guyjeangilles/raspswitch-mirror/images/partial_audio_power_circuit.jpg

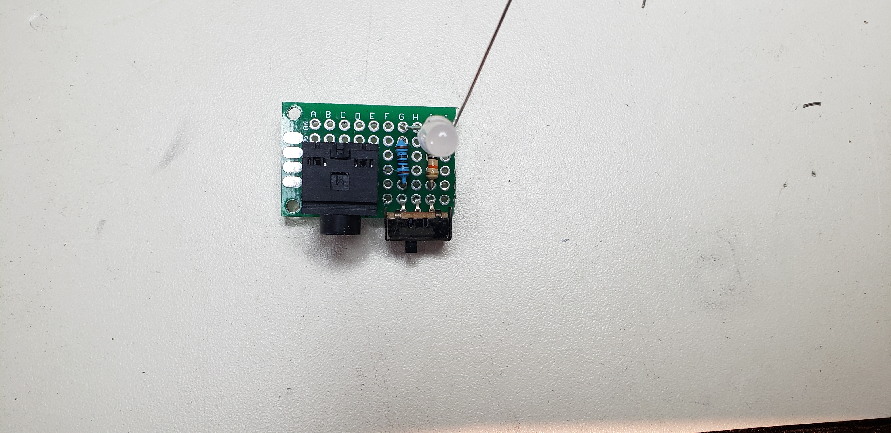
images/partial_audio_power_circuit.jpg
