guyjeangilles/raspswitch-mirror/STLs/G0011_catch_and_release_enclosure.STL

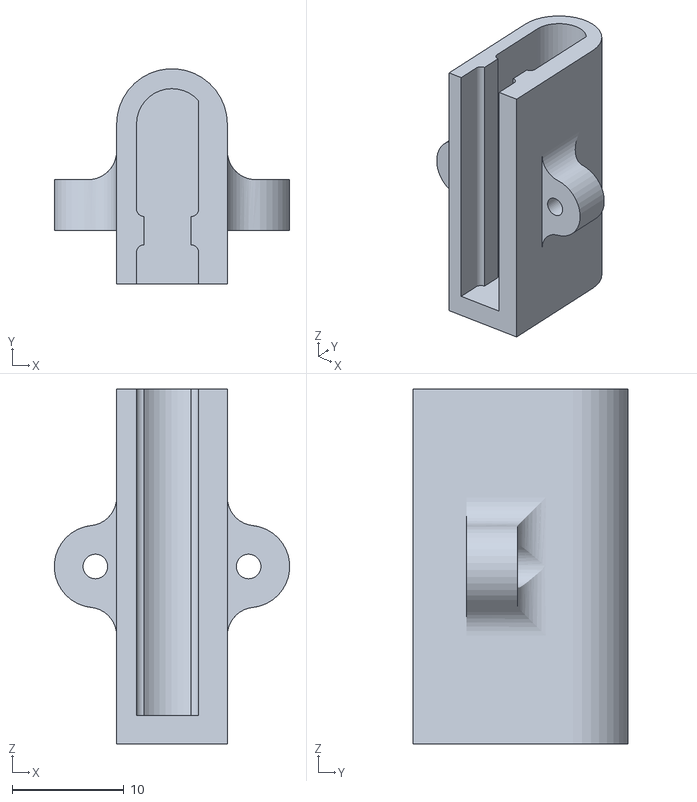
[picture p65: CAD file, 2019-10-08]
STLs/G0011_catch_and_release_enclosure.STL
21.0 x 19.2 x 31.8
