guyjeangilles/raspswitch-mirror/STEP AP203/dum_battery.step

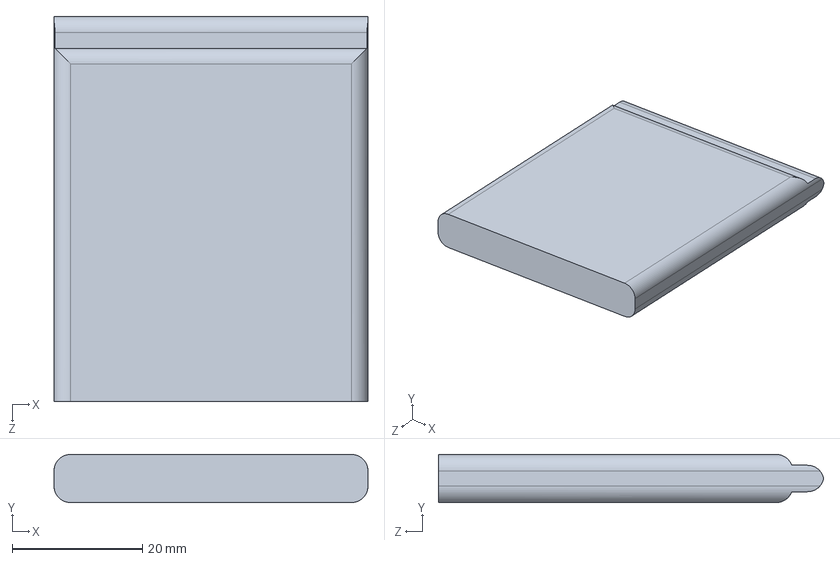
[picture p66: CAD file, 2019-10-08]
STEP AP203/dum_battery.step
48.1 x 7.38 x 59.1 mm
