guyjeangilles/raspswitch-mirror/STEP AP214/G0010_gamepad_left_top.step

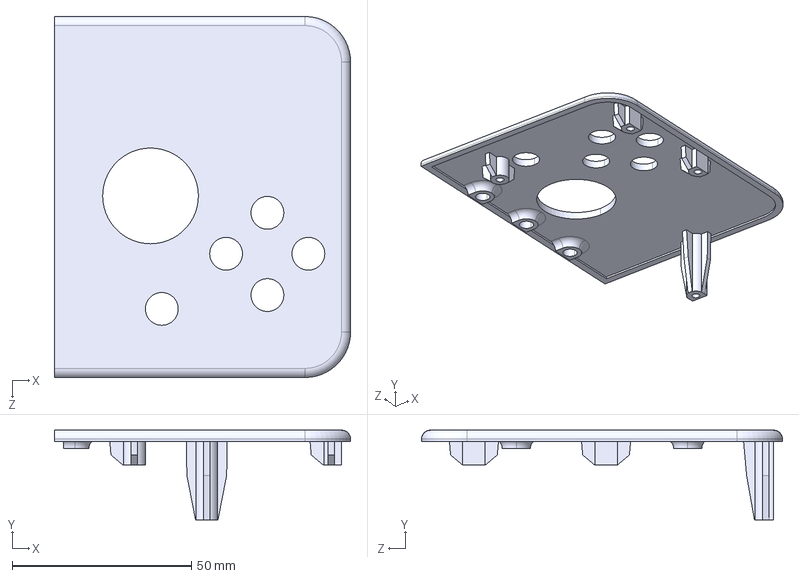
[picture p67: CAD file, 2019-10-08]
STEP AP214/G0010_gamepad_left_top.step
82.5 x 25.0 x 100.6 mm
