guyjeangilles/raspswitch-mirror/STLs/G002_dual_shaft_cap.STL

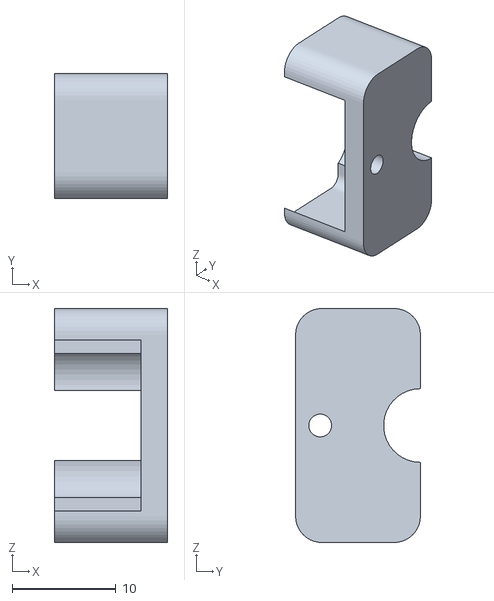
[picture p68: CAD file, 2019-10-08]
STLs/G002_dual_shaft_cap.STL
10.9 x 12.1 x 22.6
