guyjeangilles/raspswitch-mirror/STEP AP203/Molex2pinSMD.step

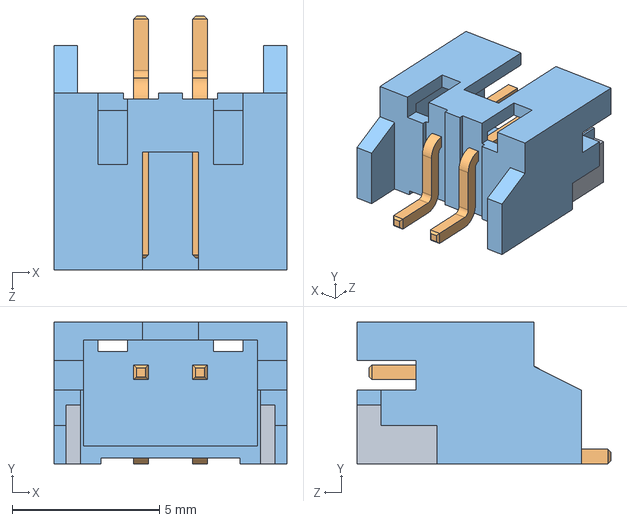
[picture p69: CAD file, 2019-10-08]
STEP AP203/Molex2pinSMD.step
7.90 x 4.80 x 8.60 mm
