guyjeangilles/raspswitch-mirror/STLs/G0009_gamepad_right_top.STL

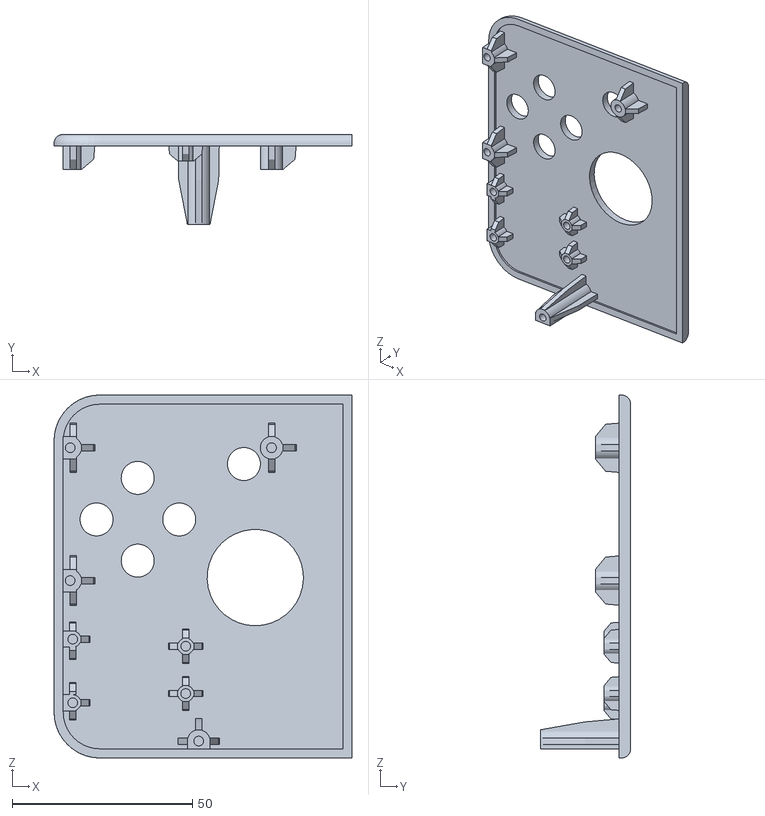
[picture p70: CAD file, 2019-10-08]
STLs/G0009_gamepad_right_top.STL
82.5 x 25.0 x 100.6
