guyjeangilles/raspswitch-mirror/STEP AP203/G0012_face_button.step

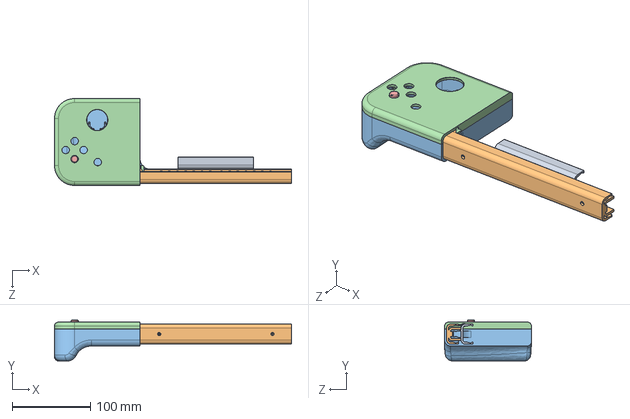
[picture p71: CAD file, 2019-10-08]
STEP AP203/G0012_face_button.step
302.3 x 52.1 x 110.8 mm
