guyjeangilles/raspswitch-mirror/STEP AP214/3.5mm_headphone_jack.step

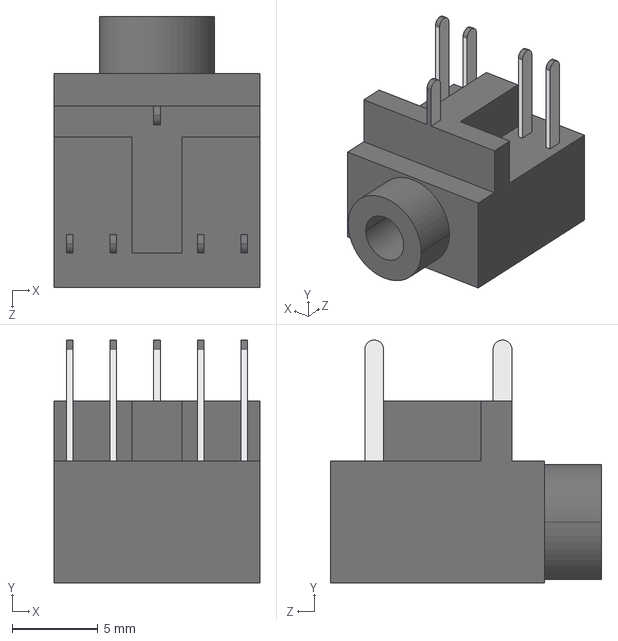
[picture p72: CAD file, 2019-10-08]
STEP AP214/3.5mm_headphone_jack.step
12.0 x 14.2 x 15.8 mm
