guyjeangilles/raspswitch-mirror/STLs/C001_top_case.STL

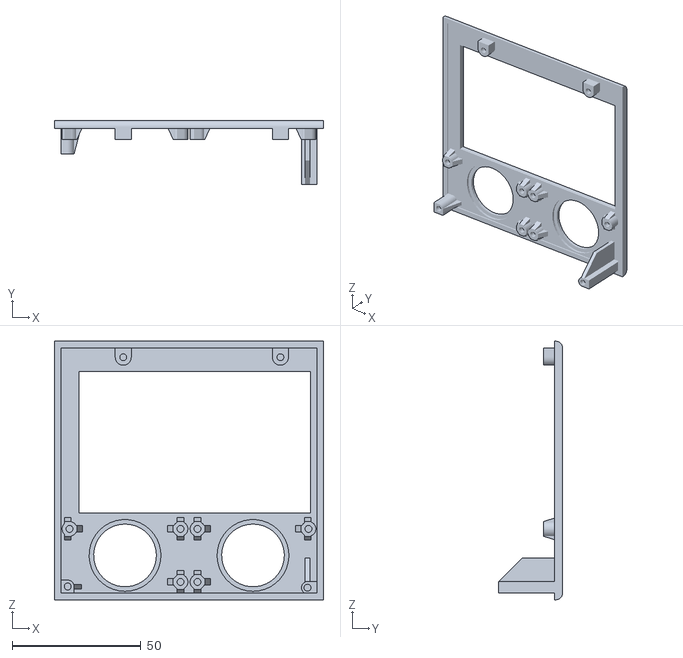
[picture p73: CAD file, 2019-10-08]
STLs/C001_top_case.STL
104.6 x 24.9 x 100.6
