guyjeangilles/raspswitch-mirror/STEP AP203/SW_PUSH_8mm002.step

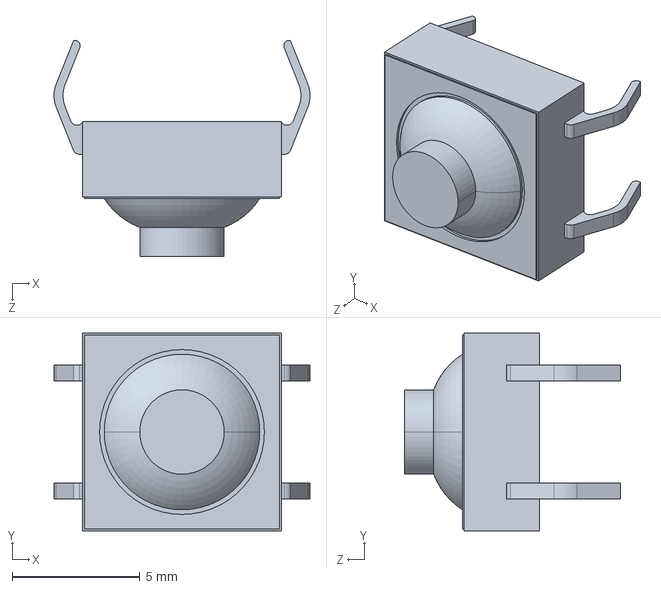
[picture p74: CAD file, 2019-10-08]
STEP AP203/SW_PUSH_8mm002.step
10.0 x 7.75 x 8.46 mm
