guyjeangilles/raspswitch-mirror/STEP AP214/stackable_header.step

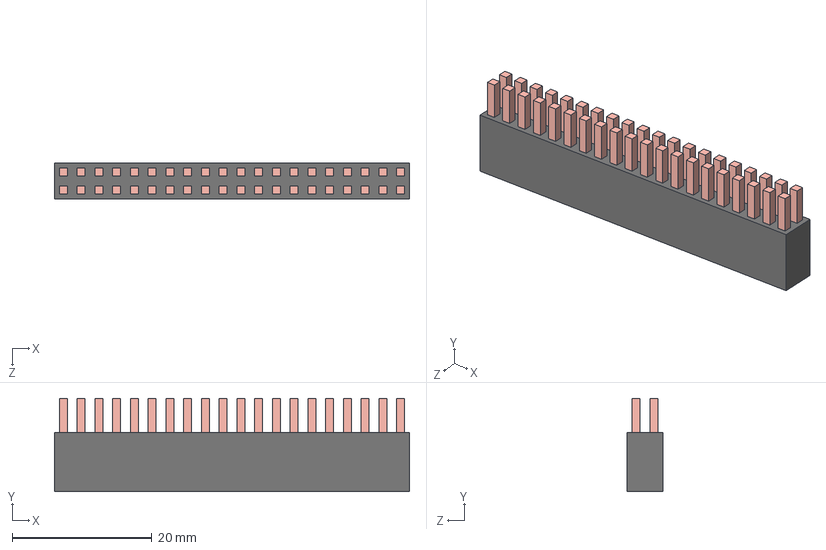
[picture p75: CAD file, 2019-10-08]
STEP AP214/stackable_header.step
50.8 x 13.3 x 5.08 mm
