guyjeangilles/raspswitch-mirror/STLs/G001_dual_shaft_bay.STL

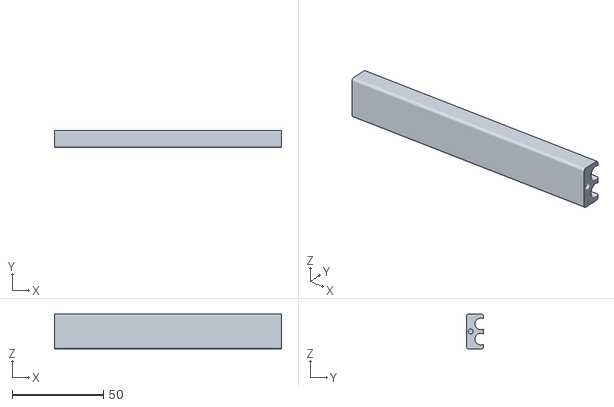
[picture p76: CAD file, 2019-10-08]
STLs/G001_dual_shaft_bay.STL
124.5 x 9.53 x 19.1
