guyjeangilles/raspswitch-mirror/STEP AP203/micro usb shell.step

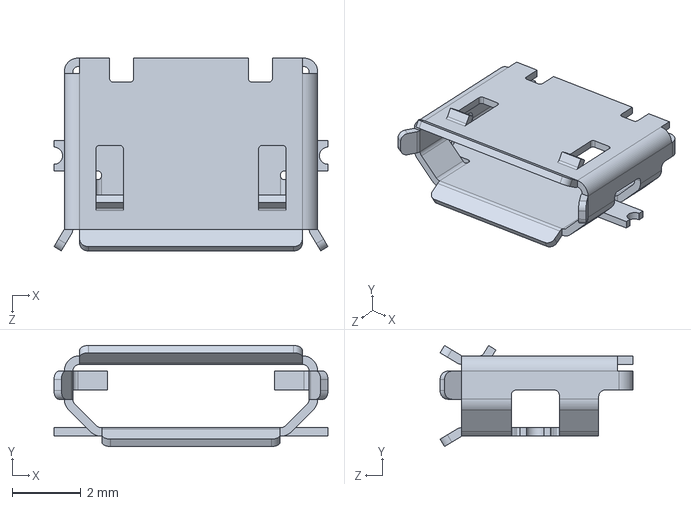
[picture p77: CAD file, 2019-10-08]
STEP AP203/micro usb shell.step
8.00 x 2.95 x 5.63 mm
