guyjeangilles/raspswitch-mirror/STLs/G0003_gamepad_left_bottom.STL

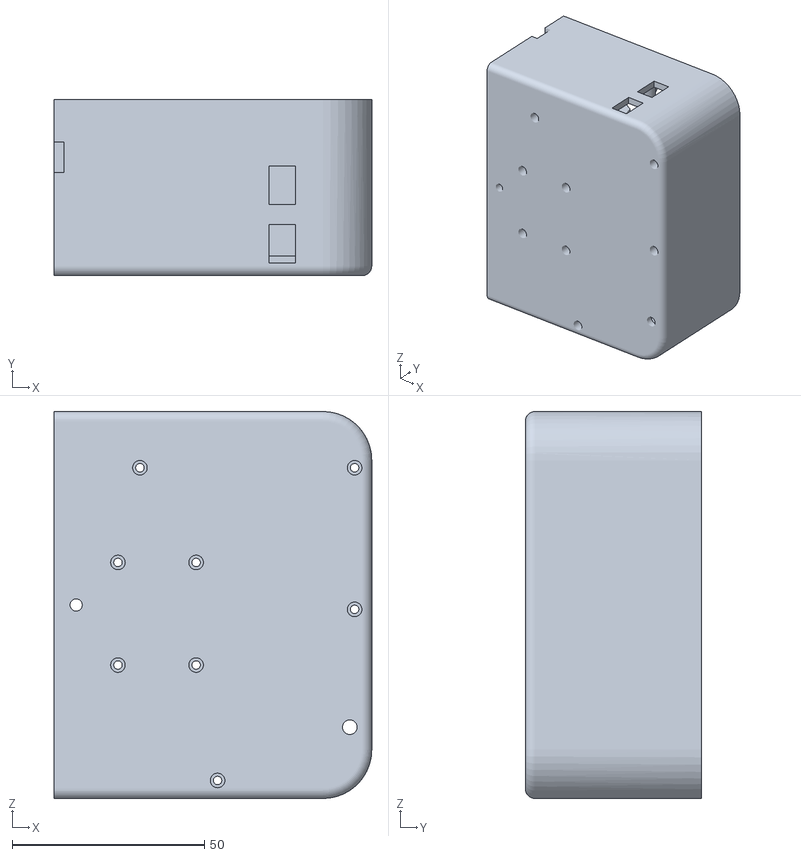
[picture p78: CAD file, 2019-10-08]
STLs/G0003_gamepad_left_bottom.STL
82.5 x 45.9 x 100.6
