guyjeangilles/raspswitch-mirror/STEP AP203/micro solid tantalum cap 22u.step

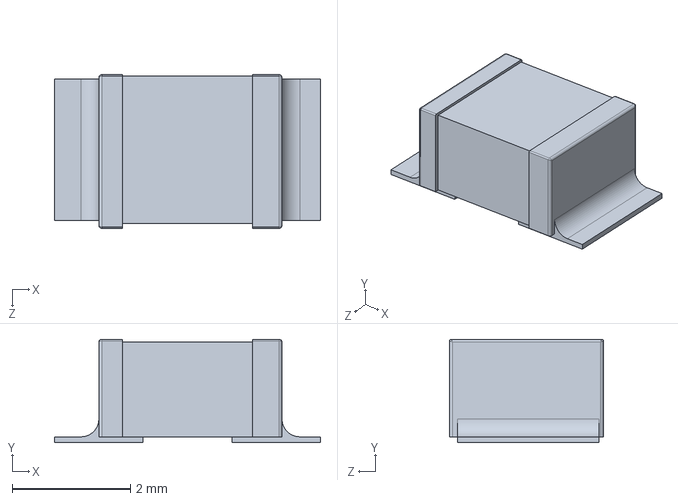
[picture p79: CAD file, 2019-10-08]
STEP AP203/micro solid tantalum cap 22u.step
4.50 x 1.75 x 2.60 mm
