guyjeangilles/raspswitch-mirror/STEP AP214/G0008_release_slide.step

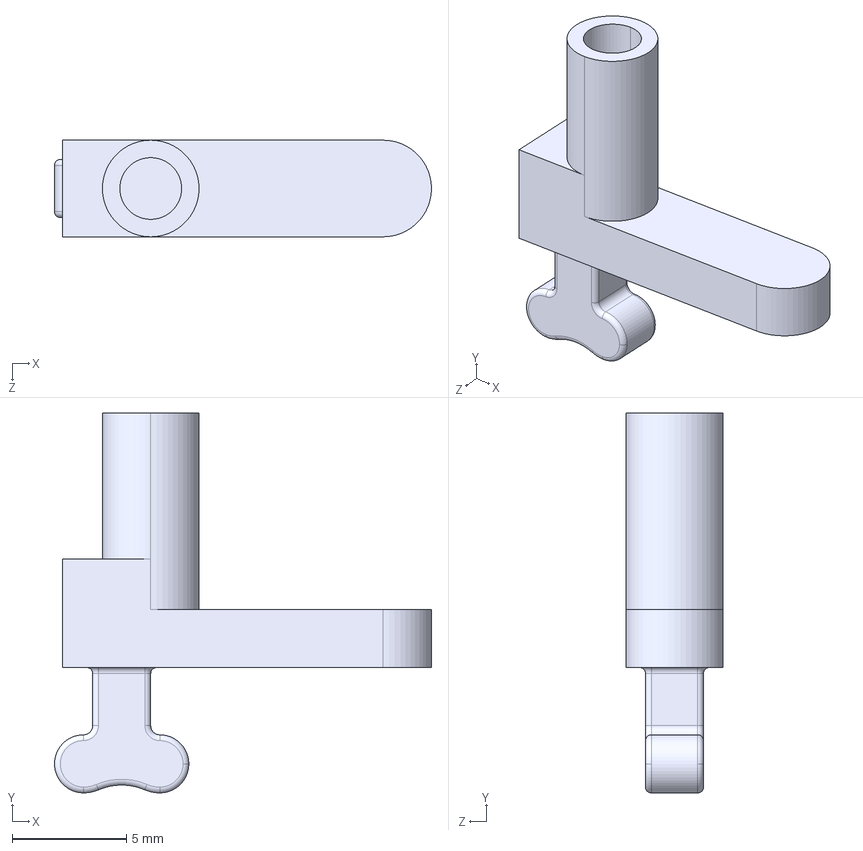
[picture p80: CAD file, 2019-10-08]
STEP AP214/G0008_release_slide.step
16.5 x 16.6 x 4.22 mm
