guyjeangilles/raspswitch-mirror/STEP AP203/speaker.step

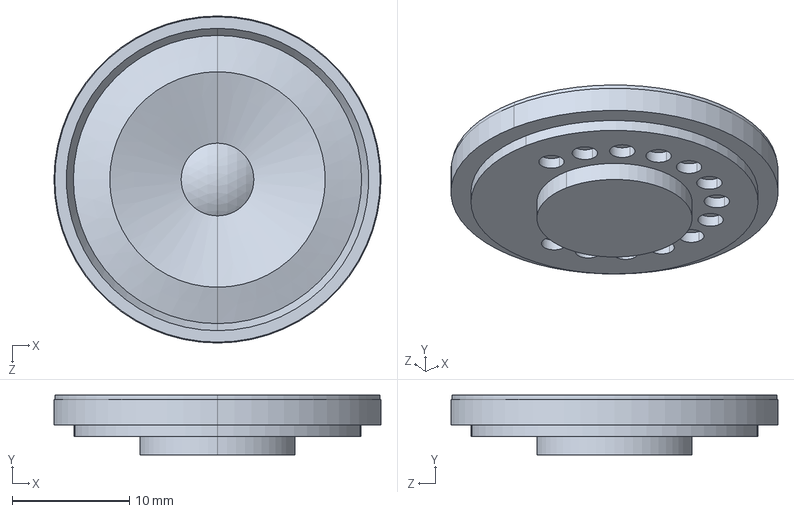
[picture p81: CAD file, 2019-10-08]
STEP AP203/speaker.step
27.9 x 5.12 x 27.9 mm
