guyjeangilles/raspswitch-mirror/STEP AP203/micro RESET.step

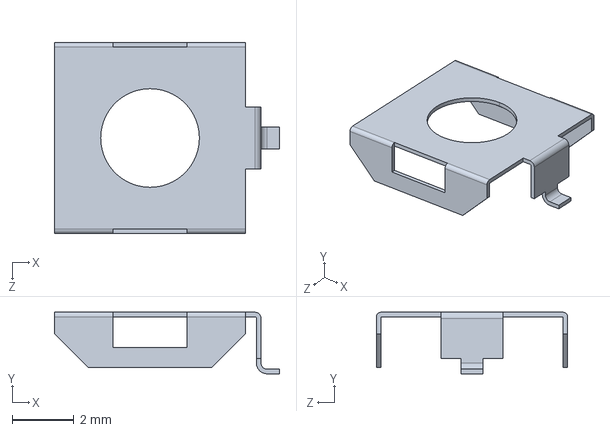
[picture p82: CAD file, 2019-10-08]
STEP AP203/micro RESET.step
7.30 x 2.00 x 6.20 mm
