guyjeangilles/raspswitch-mirror/STLs/G0004_console_catch.STL

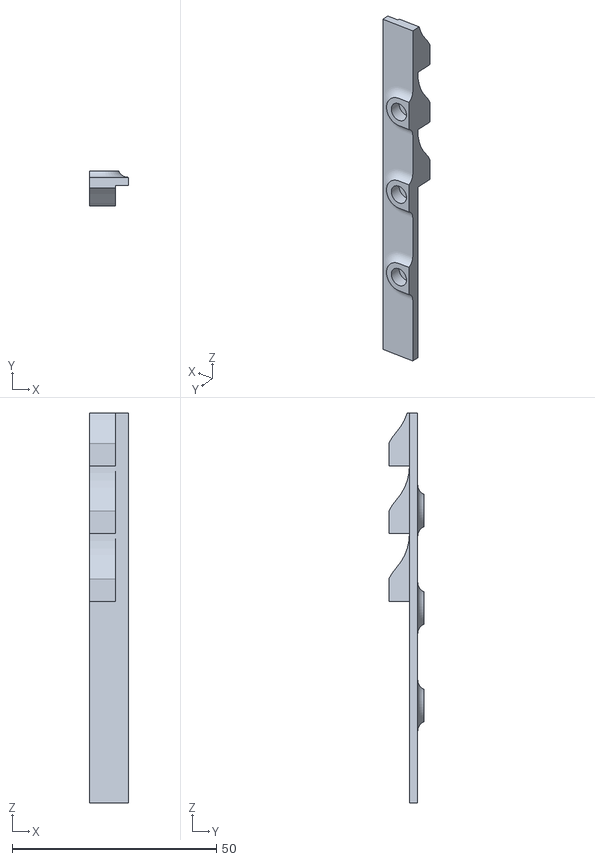
[picture p83: CAD file, 2019-10-08]
STLs/G0004_console_catch.STL
9.53 x 8.67 x 95.5
