guyjeangilles/raspswitch-mirror/STEP AP203/COMPOUND0.step

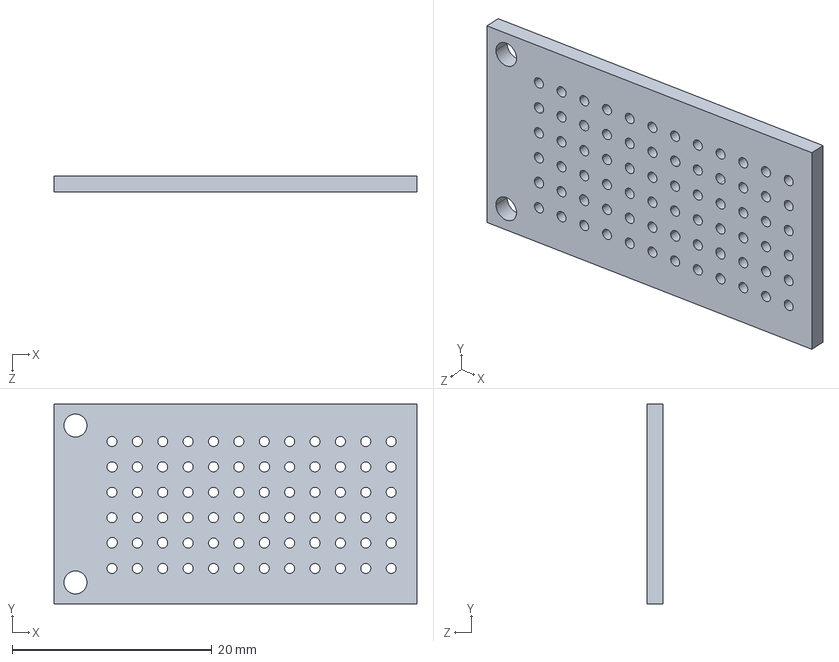
[picture p84: CAD file, 2019-10-08]
STEP AP203/COMPOUND0.step
36.3 x 20.0 x 1.60 mm
