guyjeangilles/raspswitch-mirror/STEP AP214/micro_crystal 3.2 x 2.5.step

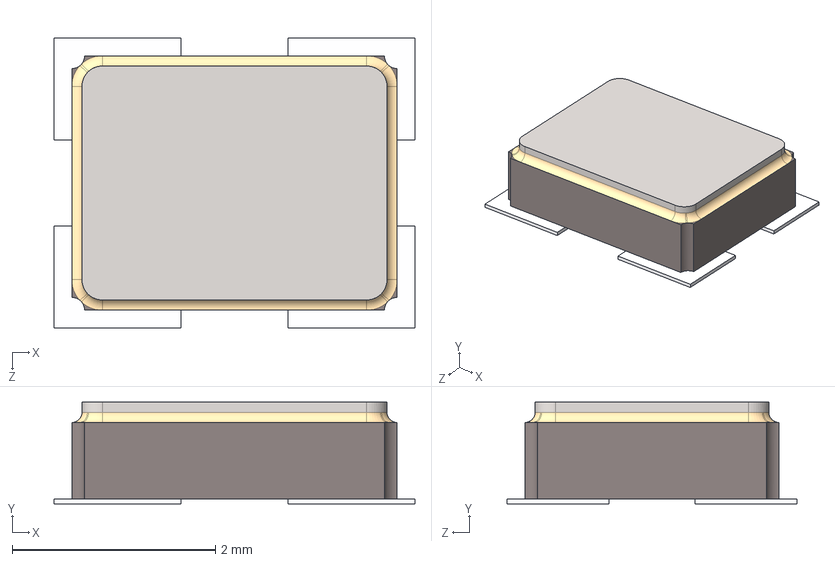
[picture p85: CAD file, 2019-10-08]
STEP AP214/micro_crystal 3.2 x 2.5.step
3.55 x 1.00 x 2.85 mm
