guyjeangilles/raspswitch-mirror/STLs/G0007_gamepad_right_bottom.STL

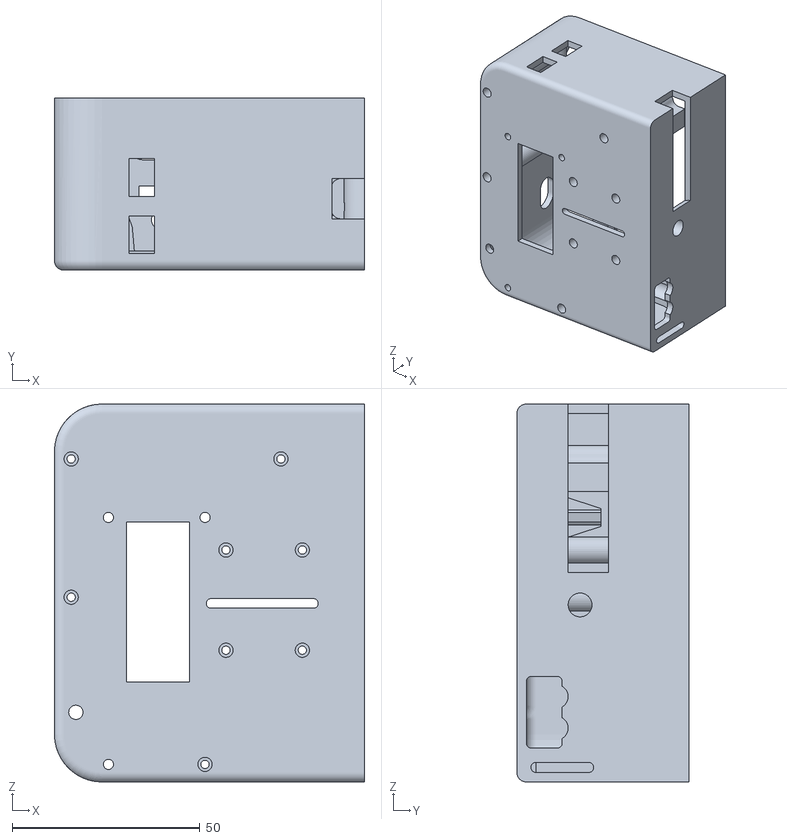
[picture p86: CAD file, 2019-10-08]
STLs/G0007_gamepad_right_bottom.STL
82.5 x 45.9 x 100.6
