guyjeangilles/raspswitch-mirror/STEP AP214/cut_2cmX8cm_protoboard.step

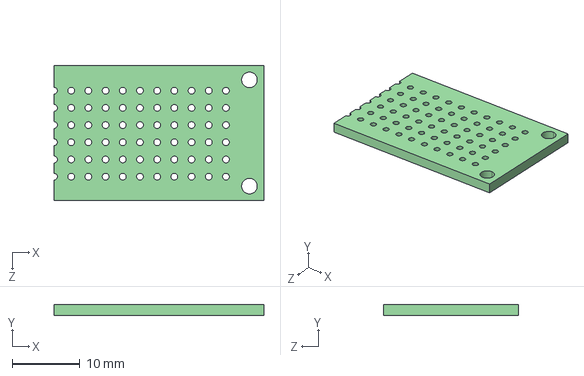
[picture p87: CAD file, 2019-10-08]
STEP AP214/cut_2cmX8cm_protoboard.step
31.0 x 1.60 x 20.0 mm
