guyjeangilles/raspswitch-mirror/STEP AP214/9032.step

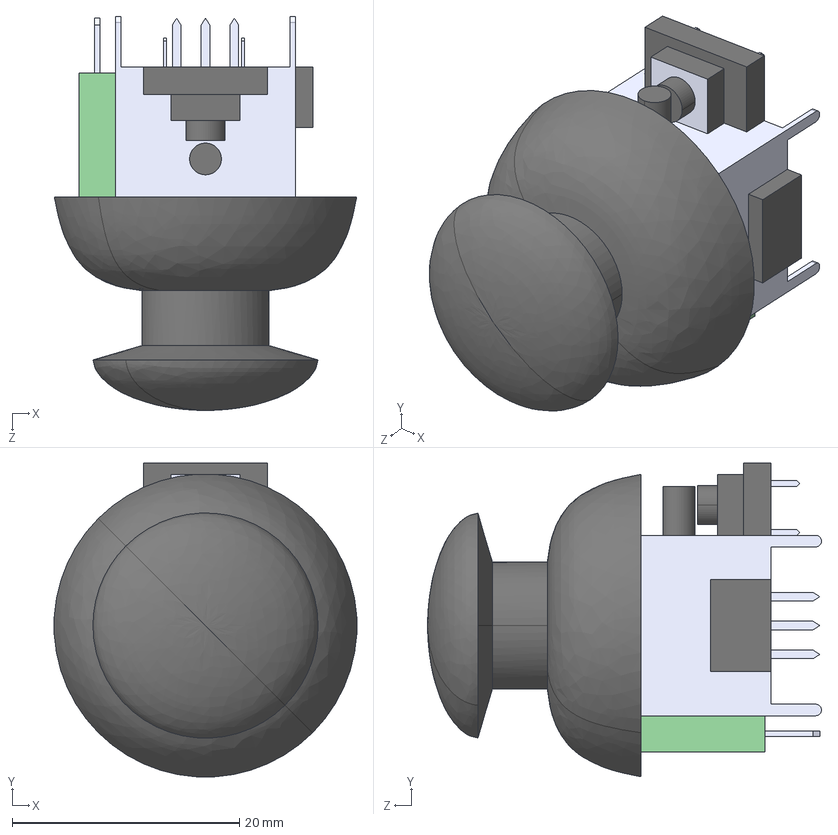
[picture p88: CAD file, 2019-10-08]
STEP AP214/9032.step
26.6 x 27.6 x 34.7 mm
