guyjeangilles/raspswitch-mirror/STEP AP203/3.5mm_plug_housing.step

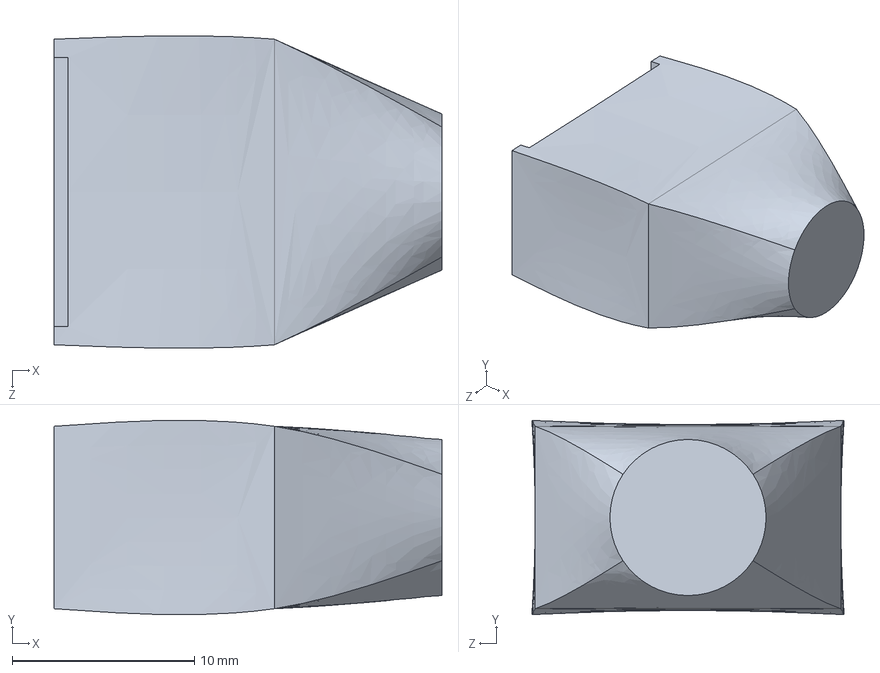
[picture p89: CAD file, 2019-10-08]
STEP AP203/3.5mm_plug_housing.step
21.3 x 10.7 x 17.1 mm
