guyjeangilles/raspswitch-mirror/STEP AP214/MO-220WGGE.step

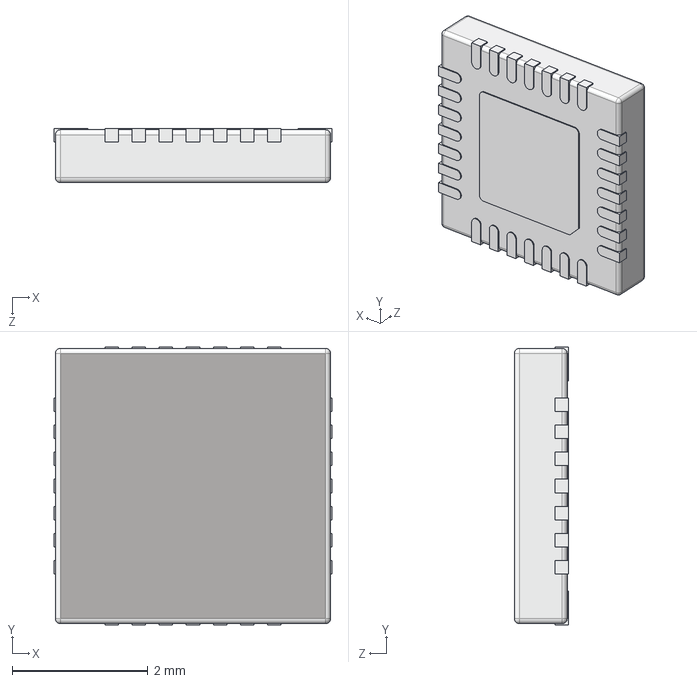
[picture p90: CAD file, 2019-10-08]
STEP AP214/MO-220WGGE.step
4.10 x 4.10 x 0.8 mm
