guyjeangilles/raspswitch-mirror/STEP AP214/Component1.step

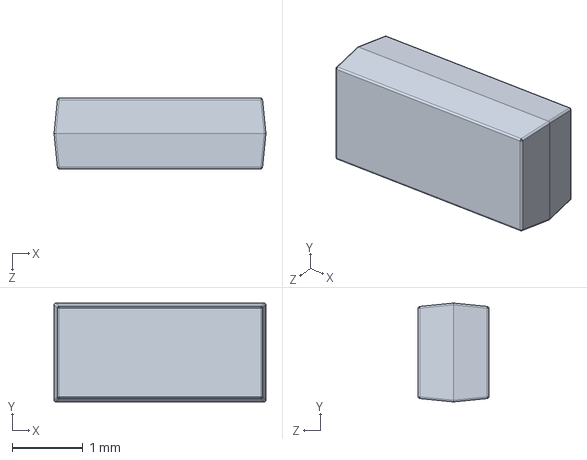
[picture p91: CAD file, 2019-10-08]
STEP AP214/Component1.step
3.00 x 1.40 x 1.00 mm
