guyjeangilles/raspswitch-mirror/STEP AP203/SOLID011.step

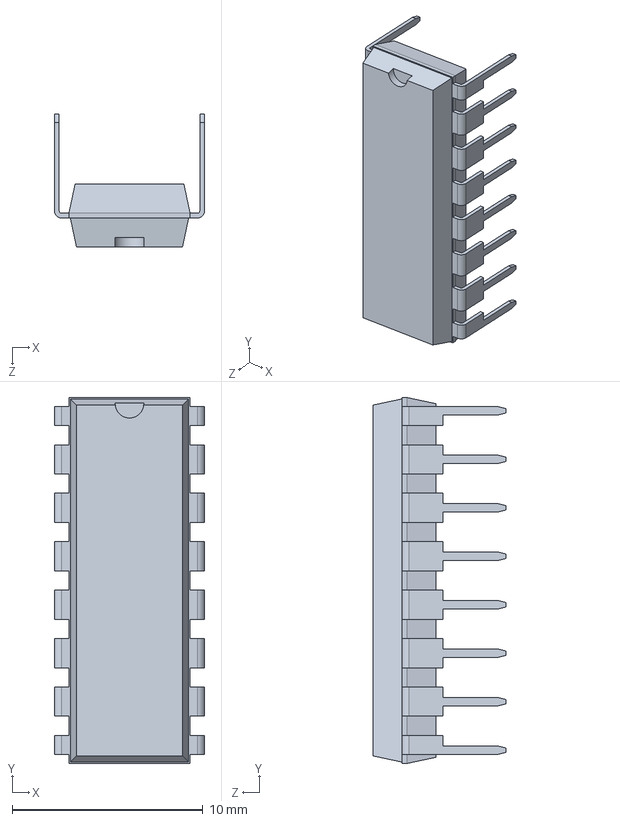
[picture p92: CAD file, 2019-10-08]
STEP AP203/SOLID011.step
7.87 x 19.2 x 6.98 mm
