guyjeangilles/raspswitch-mirror/STEP AP214/SOLID.step

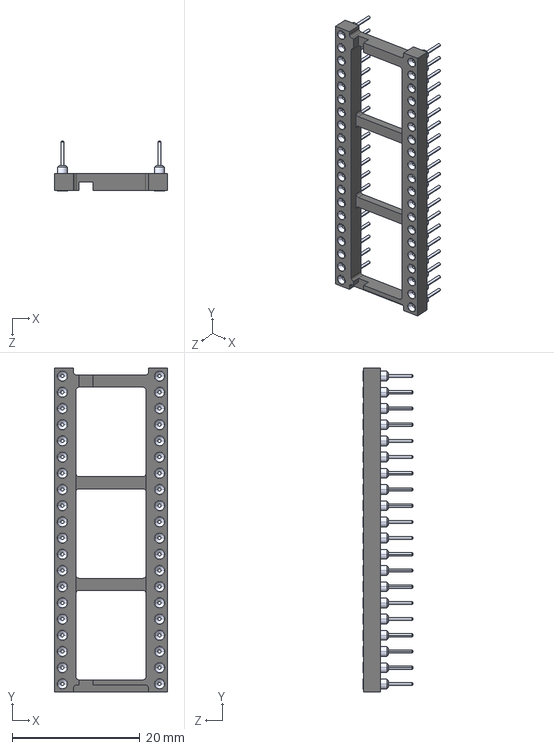
[picture p93: CAD file, 2019-10-08]
STEP AP214/SOLID.step
17.8 x 50.8 x 7.79 mm
