guyjeangilles/raspswitch-mirror/STEP AP214/thumb_joystick+breakout.step

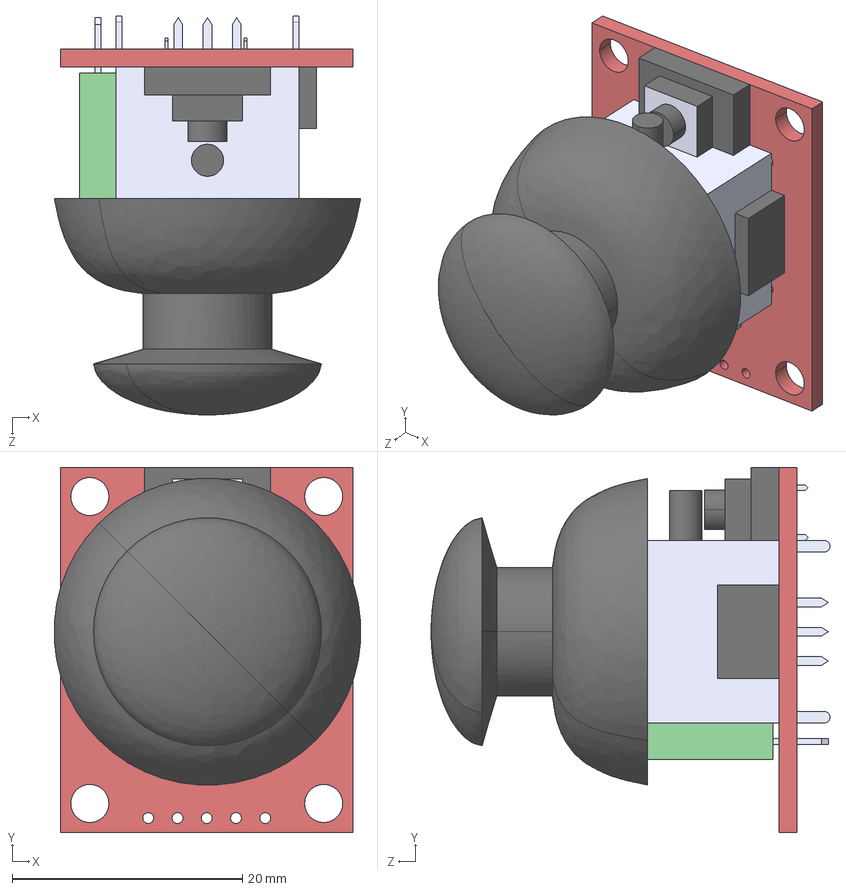
[picture p94: CAD file, 2019-10-08]
STEP AP214/thumb_joystick+breakout.step
26.6 x 31.8 x 34.7 mm
joystick-breakout_import
