guyjeangilles/raspswitch-mirror/STEP AP203/right_angle_slide_switch_EG1218.step

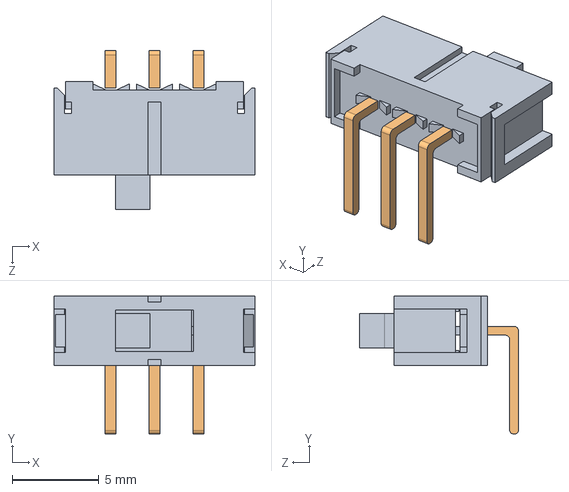
[picture p95: CAD file, 2019-10-08]
STEP AP203/right_angle_slide_switch_EG1218.step
11.6 x 7.95 x 9.18 mm
