guyjeangilles/raspswitch-mirror/STEP AP214/MO-229W3030D-1_4000.step

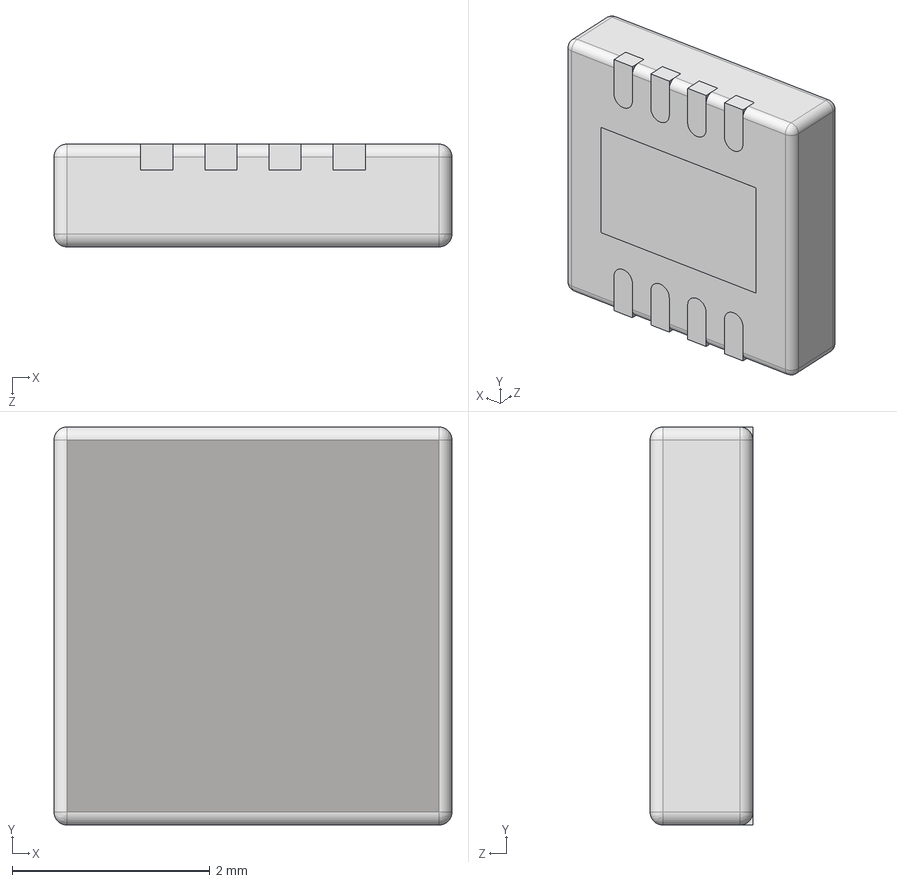
[picture p96: CAD file, 2019-10-08]
STEP AP214/MO-229W3030D-1_4000.step
4.03 x 4.03 x 1.04 mm
