guyjeangilles/raspswitch-mirror/STEP AP214/COMPOUND001.step

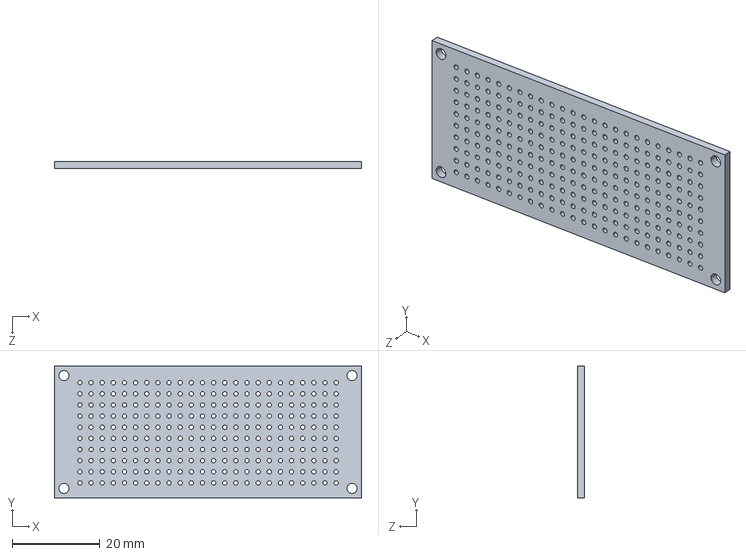
[picture p97: CAD file, 2019-10-08]
STEP AP214/COMPOUND001.step
70.0 x 30.0 x 1.60 mm
