guyjeangilles/raspswitch-mirror/STEP AP214/3.5_plug_terminal_block.step

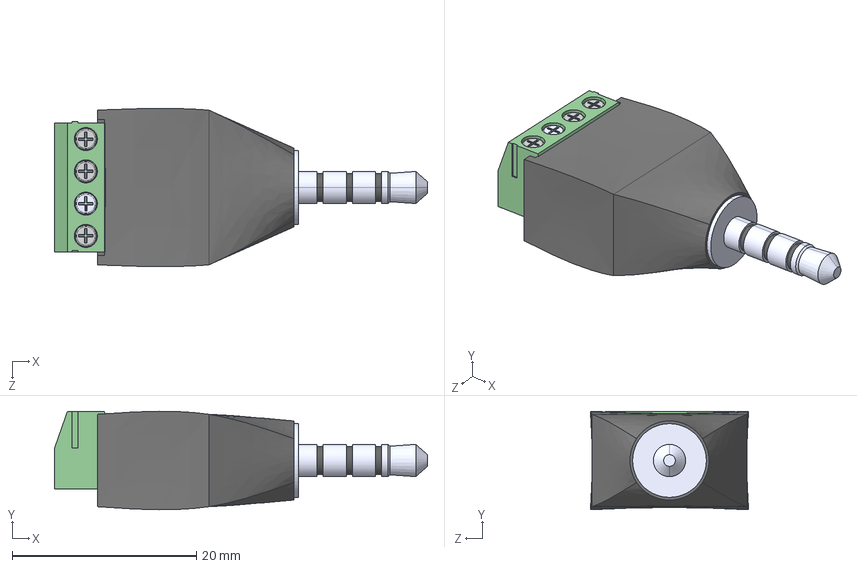
[picture p98: CAD file, 2019-10-08]
STEP AP214/3.5_plug_terminal_block.step
40.5 x 10.7 x 17.2 mm
3.5mm_plug_housing
3.5mm Plug
Screw Terminal Block 3.5mm 4-way_6
Screw Terminal Block 3.5mm 4-way_5
Screw Terminal Block 3.5mm 4-way
Screw Terminal Block 3.5mm 4-way_10
Screw Terminal Block 3.5mm 4-way_9
Screw Terminal Block 3.5mm 4-way_2
Screw Terminal Block 3.5mm 4-way_11
Screw Terminal Block 3.5mm 4-way_3
Screw Terminal Block 3.5mm 4-way_7
