guyjeangilles/raspswitch-mirror/STEP AP214/FD-5wsrgb-A_no_leads.step

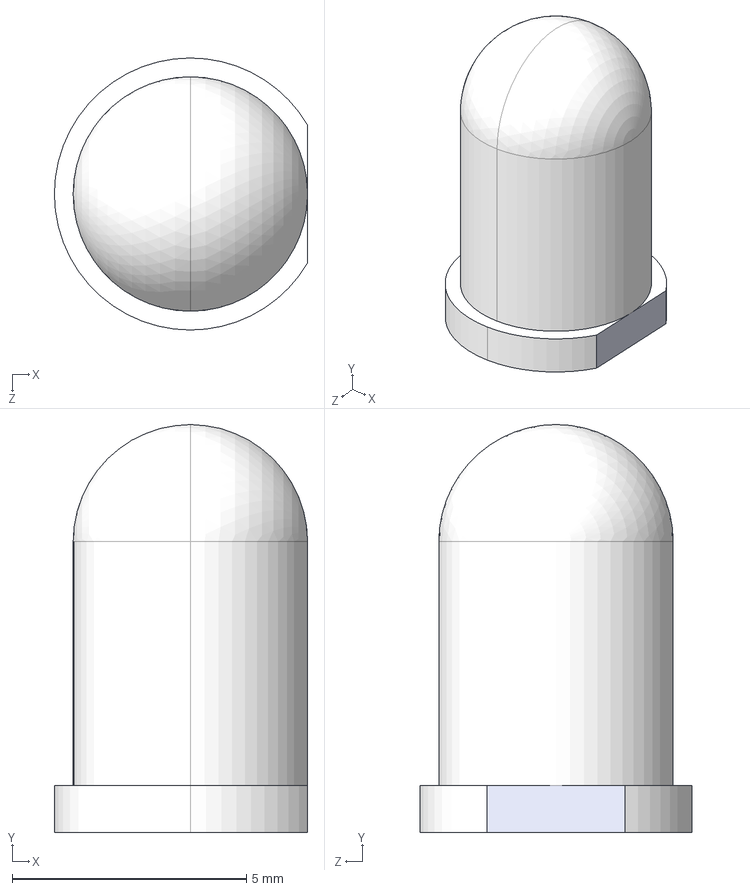
[picture p99: CAD file, 2019-10-08]
STEP AP214/FD-5wsrgb-A_no_leads.step
5.40 x 8.70 x 5.80 mm
