guyjeangilles/raspswitch-mirror/STEP AP203/DIP_16_W7_62mm_Socket.step

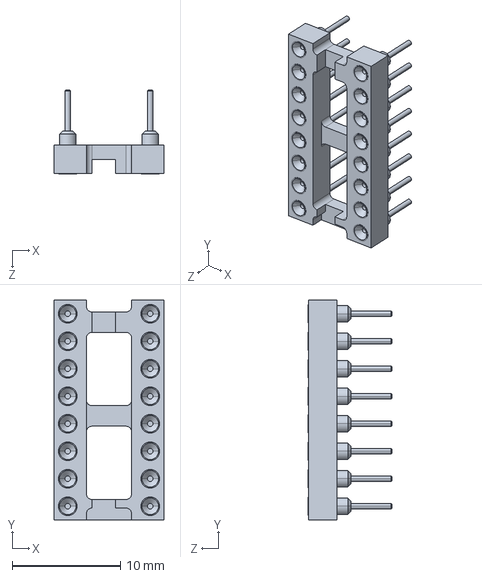
[picture p100: CAD file, 2019-10-08]
STEP AP203/DIP_16_W7_62mm_Socket.step
10.2 x 20.3 x 7.79 mm
