guyjeangilles/raspswitch-mirror/STEP AP203/micro usb internal.step

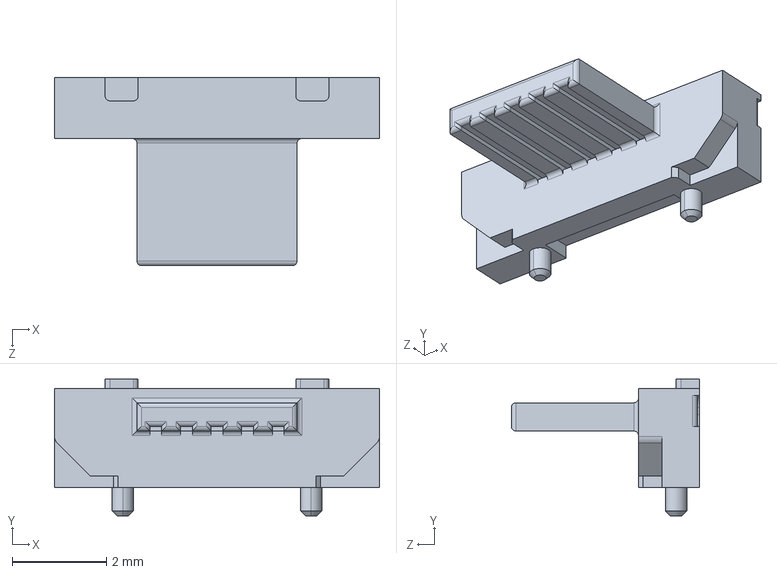
[picture p101: CAD file, 2019-10-08]
STEP AP203/micro usb internal.step
6.90 x 2.90 x 4.00 mm
