guyjeangilles/raspswitch-mirror/STEP AP214/c0402.step

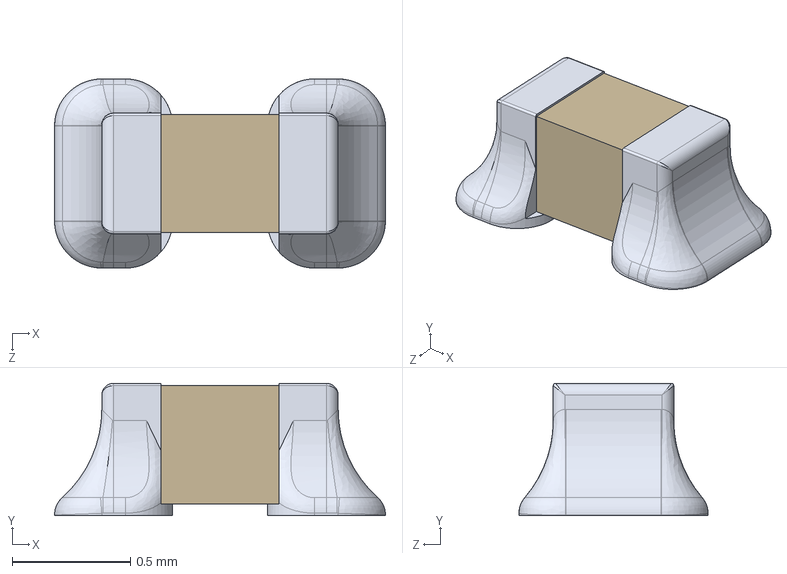
[picture p102: CAD file, 2019-10-08]
STEP AP214/c0402.step
1.40 x 0.56 x 0.8 mm
