guyjeangilles/raspswitch-mirror/STEP AP214/micro RESET CORE.step

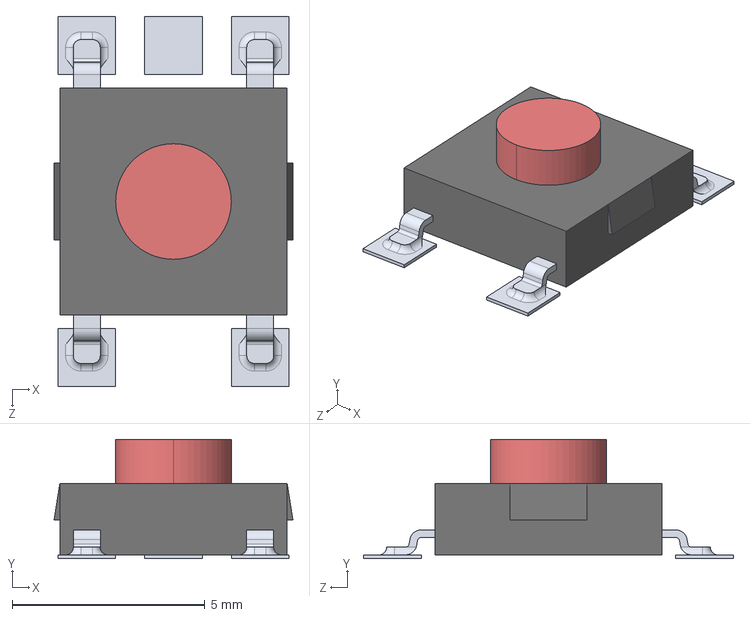
[picture p103: CAD file, 2019-10-08]
STEP AP214/micro RESET CORE.step
6.20 x 3.10 x 9.60 mm
