guyjeangilles/raspswitch-mirror/STEP AP214/MICRO_DIODE CD1206-S01575.step

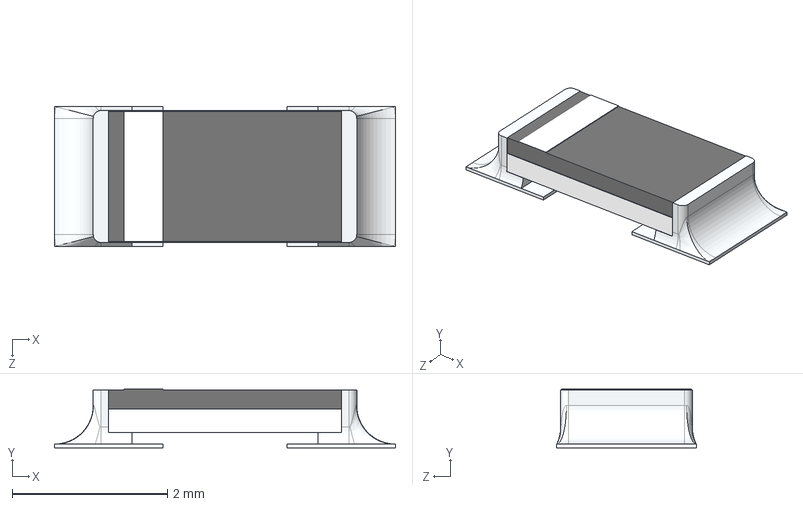
[picture p104: CAD file, 2019-10-08]
STEP AP214/MICRO_DIODE CD1206-S01575.step
4.40 x 0.76 x 1.80 mm
