guyjeangilles/raspswitch-mirror/STEP AP203/right_shoulder_pcb.step

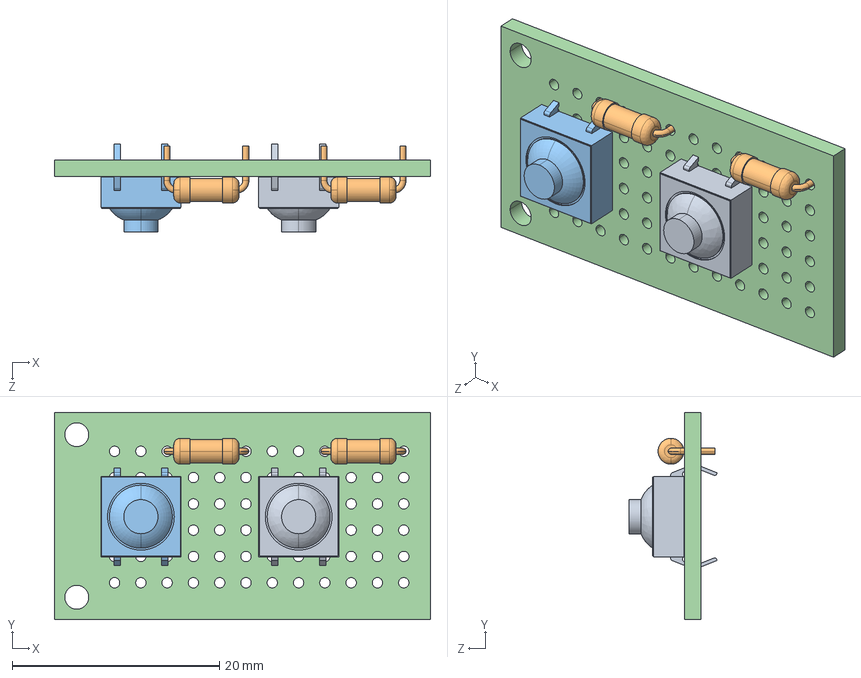
[picture p105: CAD file, 2019-10-08]
STEP AP203/right_shoulder_pcb.step
36.3 x 20.0 x 8.46 mm
Tactal Switch -SOFT -Thru (8mmx 8mmx5.45mm)
