guyjeangilles/raspswitch-mirror/STEP AP214/sot23.step

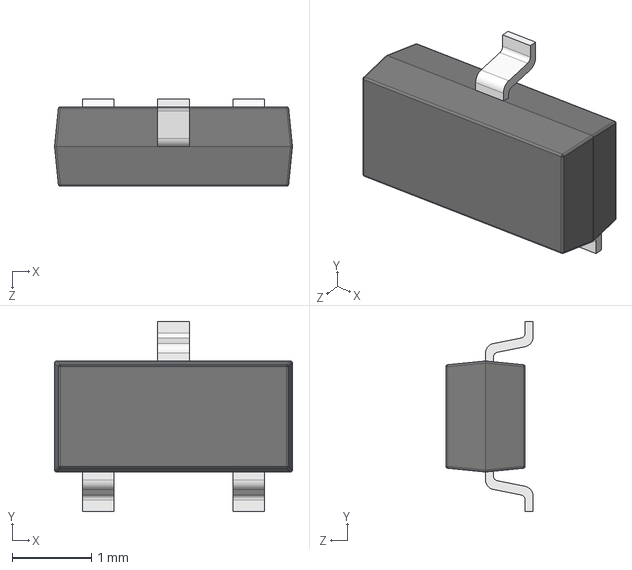
[picture p106: CAD file, 2019-10-08]
STEP AP214/sot23.step
3.00 x 2.40 x 1.10 mm
pin x 3
