guyjeangilles/raspswitch-mirror/STEP AP203/joystick-breakout_import.step

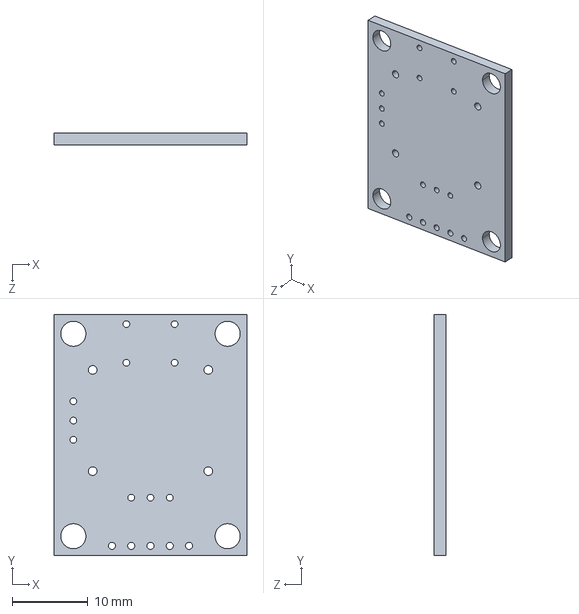
[picture p107: CAD file, 2019-10-08]
STEP AP203/joystick-breakout_import.step
25.4 x 31.8 x 1.59 mm
