guyjeangilles/raspswitch-mirror/STEP AP203/atmega32U4.step

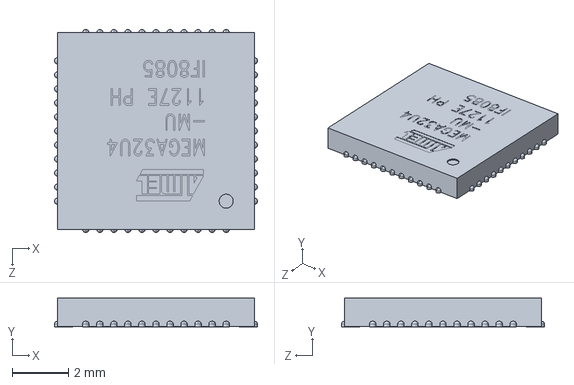
[picture p108: CAD file, 2019-10-08]
STEP AP203/atmega32U4.step
7.23 x 1.02 x 7.23 mm
