guyjeangilles/raspswitch-mirror/STEP AP214/MicroUSB_best.step

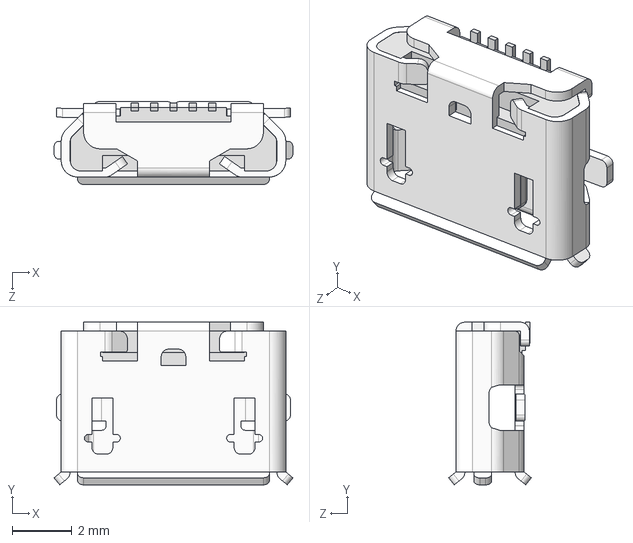
[picture p109: CAD file, 2019-10-08]
STEP AP214/MicroUSB_best.step
7.98 x 5.43 x 2.76 mm
