guyjeangilles/raspswitch-mirror/STEP AP203/arduino micro board.step

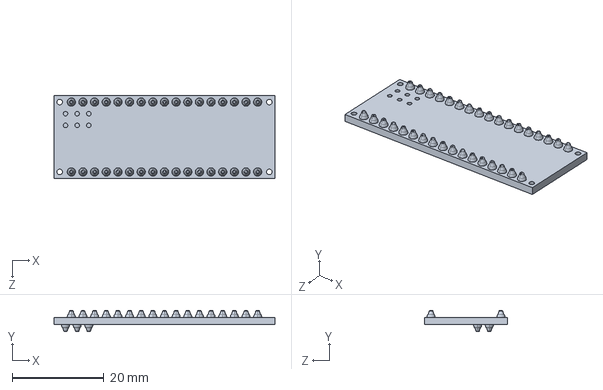
[picture p110: CAD file, 2019-10-08]
STEP AP203/arduino micro board.step
48.2 x 4.60 x 18.0 mm
