guyjeangilles/raspswitch-mirror/STEP AP214/15mm_M2.5_standoff.step

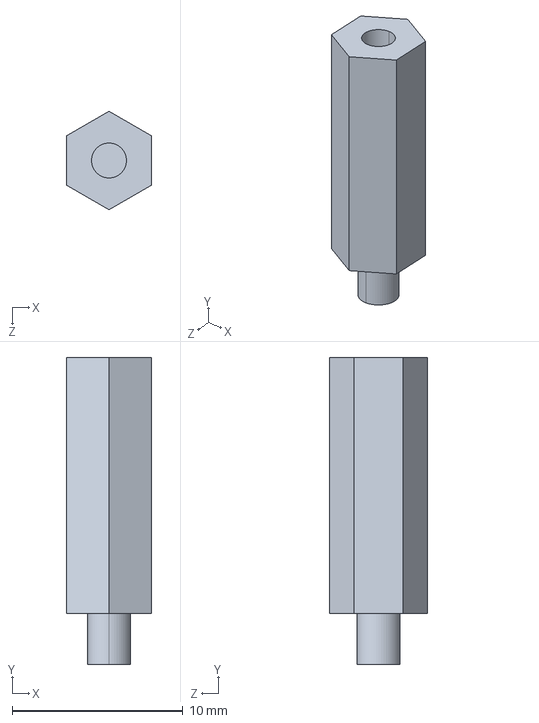
[picture p111: CAD file, 2019-10-08]
STEP AP214/15mm_M2.5_standoff.step
5.00 x 18.0 x 5.77 mm
