guyjeangilles/raspswitch-mirror/STEP AP214/headphone_jack_pcb.step

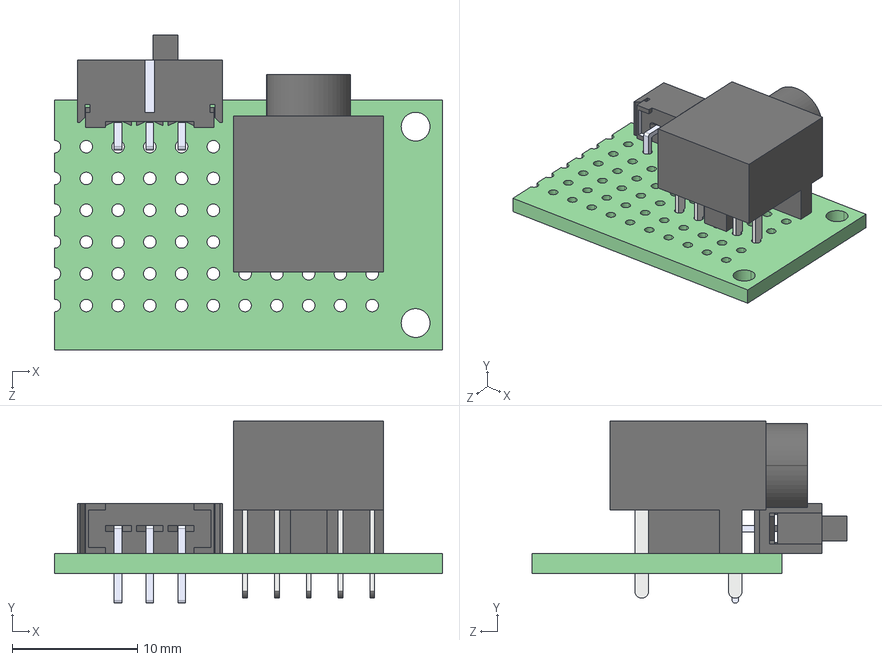
[picture p112: CAD file, 2019-10-08]
STEP AP214/headphone_jack_pcb.step
31.0 x 14.5 x 25.2 mm
cut_2cmX8cm_protoboard
3.5mm_headphone_jack
right_angle_slide_switch_EG1218
