guyjeangilles/raspswitch-mirror/STEP AP203/MICRO - reg.step

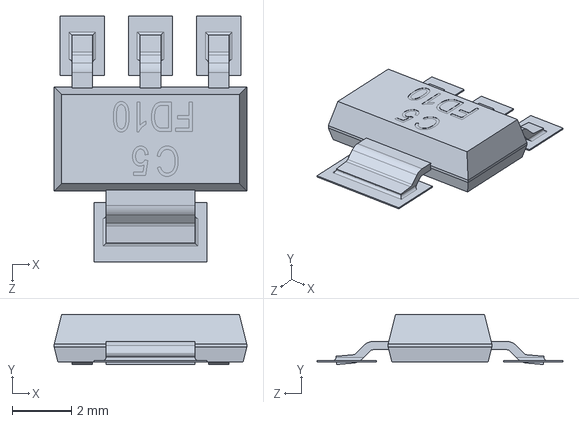
[picture p113: CAD file, 2019-10-08]
STEP AP203/MICRO - reg.step
6.50 x 1.69 x 8.30 mm
