guyjeangilles/raspswitch-mirror/STEP AP203/right_angle_hdmi.step

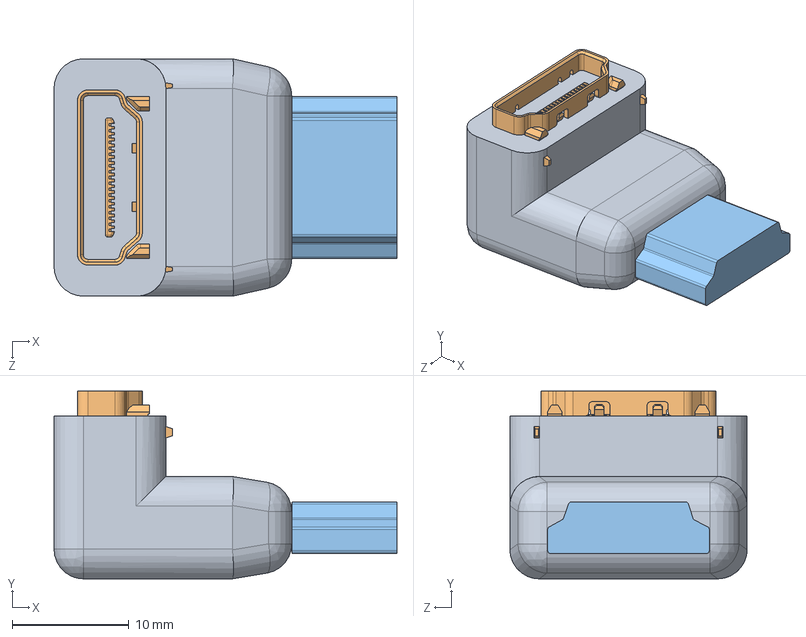
[picture p114: CAD file, 2019-10-08]
STEP AP203/right_angle_hdmi.step
29.3 x 16.1 x 20.3 mm
right_angle_hdmi_housing
10029449-111RLF_hdmi_recepticale
dum_hdmi_male
