guyjeangilles/raspswitch-mirror/STEP AP214/COMPOUND.step

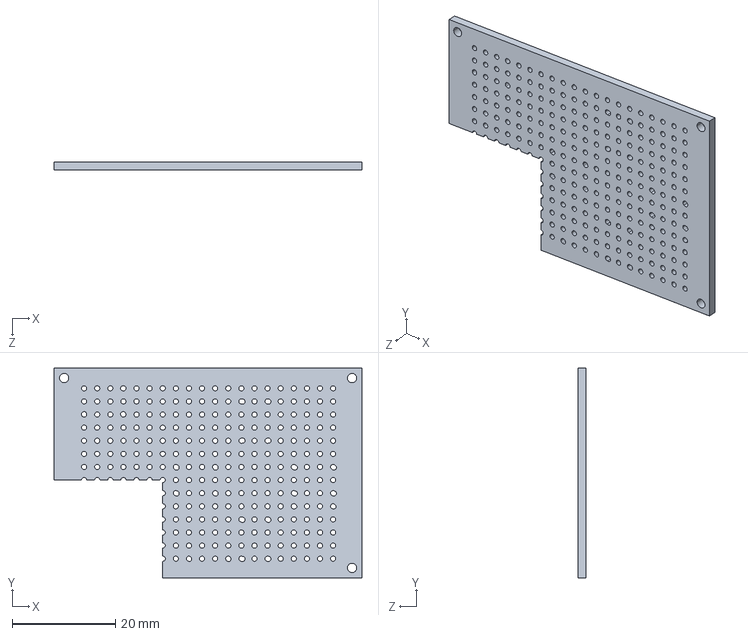
[picture p115: CAD file, 2019-10-08]
STEP AP214/COMPOUND.step
59.7 x 40.6 x 1.60 mm
