guyjeangilles/raspswitch-mirror/STEP AP203/micro RESET BUTTON.step

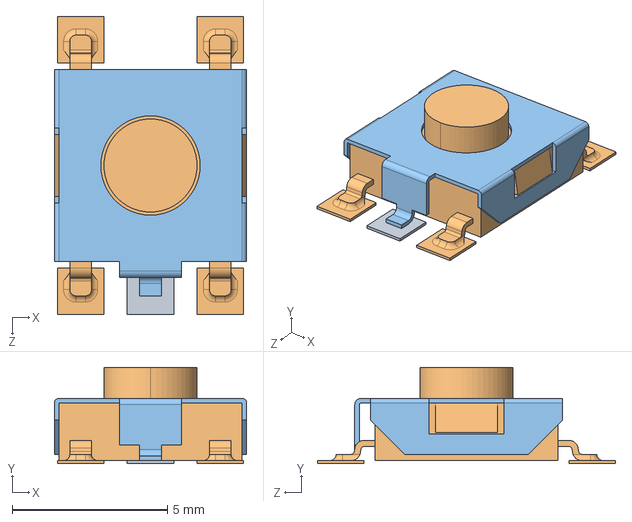
[picture p116: CAD file, 2019-10-08]
STEP AP203/micro RESET BUTTON.step
6.20 x 3.10 x 9.60 mm
micro RESET CORE
micro RESET
