guyjeangilles/raspswitch-mirror/STEP AP214/MICRO_220 RESISTOR PACK.step

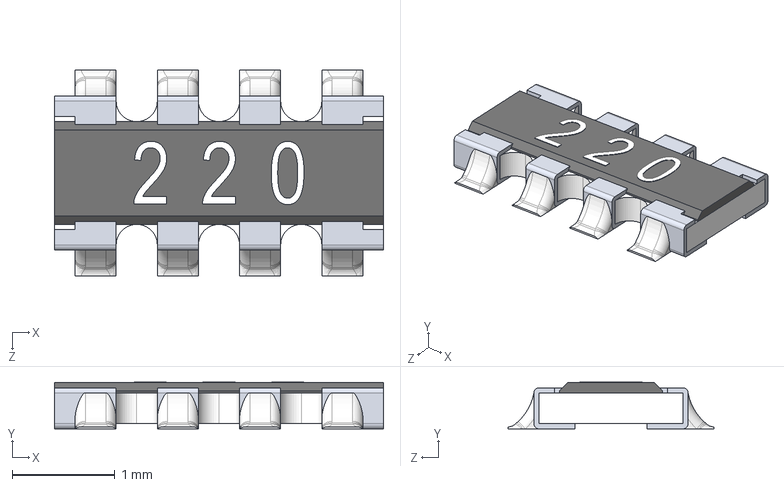
[picture p117: CAD file, 2019-10-08]
STEP AP214/MICRO_220 RESISTOR PACK.step
3.20 x 0.455 x 2.00 mm
