guyjeangilles/raspswitch-mirror/STEP AP214/right_angle_hdmi_housing.step

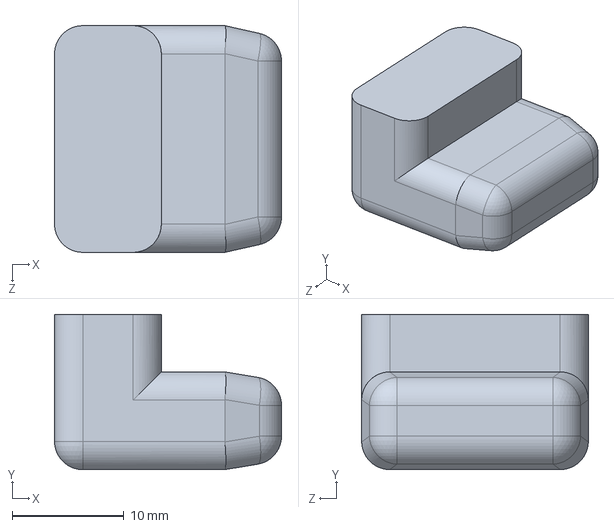
[picture p118: CAD file, 2019-10-08]
STEP AP214/right_angle_hdmi_housing.step
20.3 x 13.9 x 20.3 mm
