guyjeangilles/raspswitch-mirror/STEP AP203/micro usb contact.step

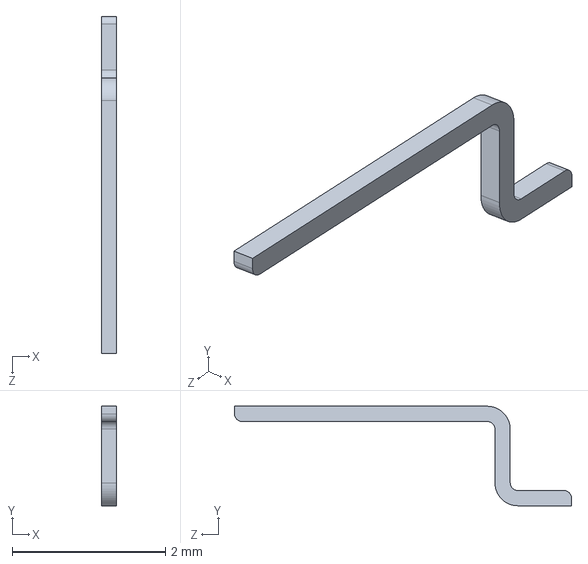
[picture p119: CAD file, 2019-10-08]
STEP AP203/micro usb contact.step
0.2 x 1.30 x 4.40 mm
