guyjeangilles/raspswitch-mirror/STEP AP203/dum_blueSMIRF.step

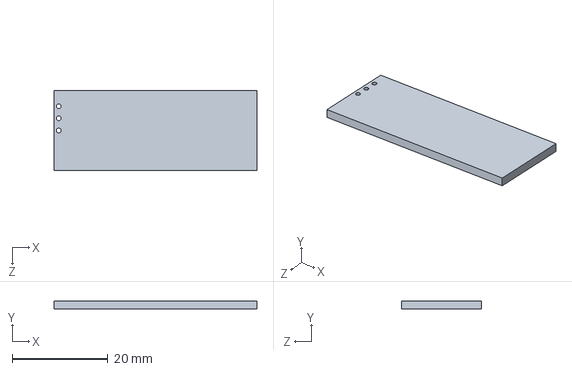
[picture p120: CAD file, 2019-10-08]
STEP AP203/dum_blueSMIRF.step
42.5 x 1.71 x 16.7 mm
