guyjeangilles/raspswitch-mirror/STEP AP203/MH2029-300Y.step

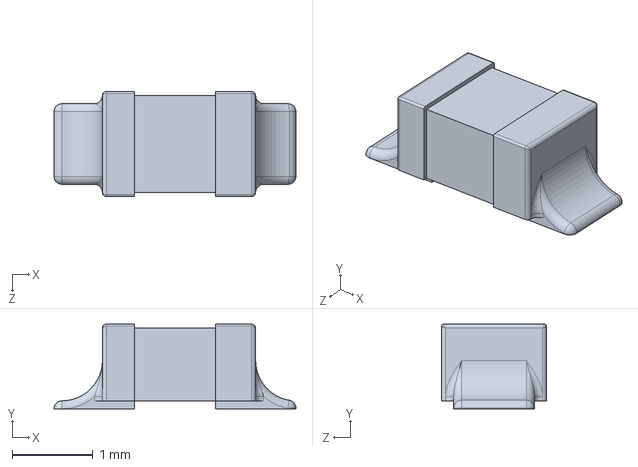
[picture p121: CAD file, 2019-10-08]
STEP AP203/MH2029-300Y.step
3.00 x 1.05 x 1.30 mm
