guyjeangilles/raspswitch-mirror/STEP AP214/micro mf-msmf050-2.step

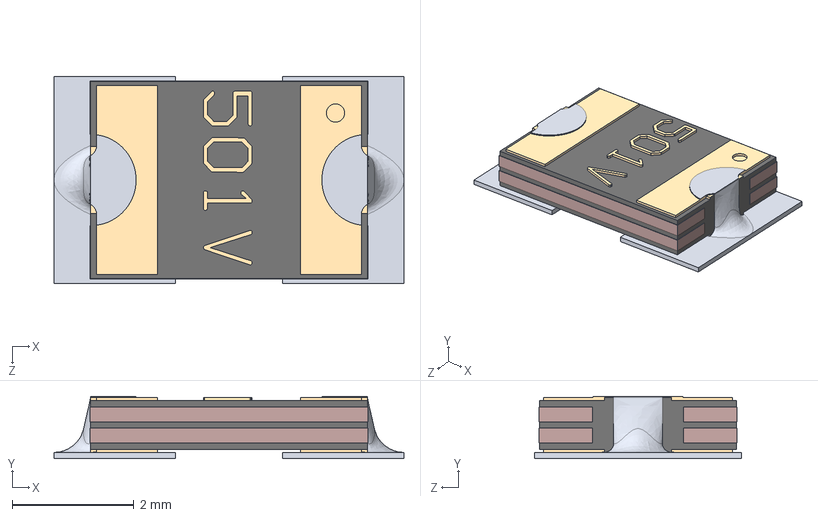
[picture p122: CAD file, 2019-10-08]
STEP AP214/micro mf-msmf050-2.step
5.75 x 1.02 x 3.40 mm
