guyjeangilles/raspswitch-mirror/STEP AP203/CAPC-0805-T0.75-BN.step

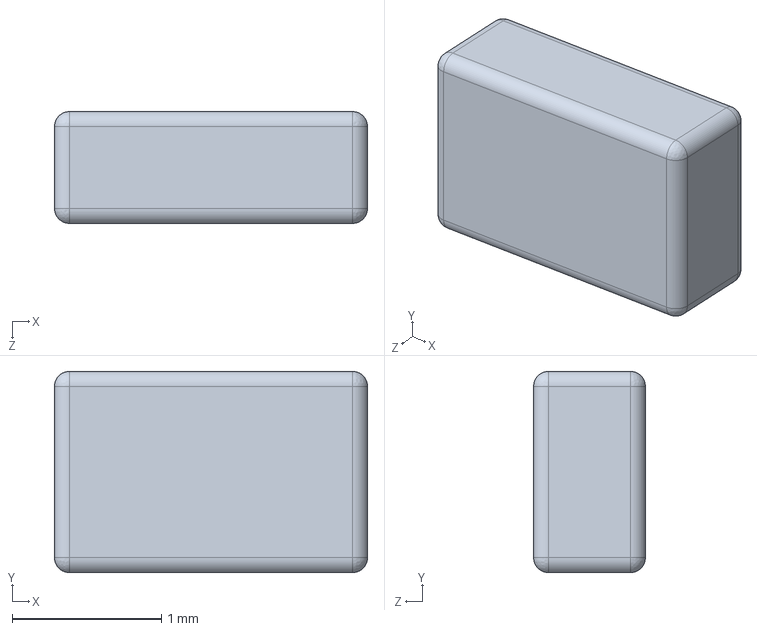
[picture p123: CAD file, 2019-10-08]
STEP AP203/CAPC-0805-T0.75-BN.step
2.10 x 1.35 x 0.75 mm
