guyjeangilles/raspswitch-mirror/STEP AP203/hyperpixel4.0.step

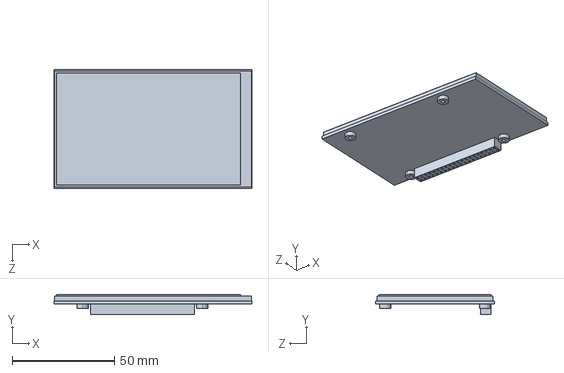
[picture p124: CAD file, 2019-10-08]
STEP AP203/hyperpixel4.0.step
97.0 x 10.0 x 58.5 mm
