guyjeangilles/raspswitch-mirror/STEP AP203/micro ssot3.step

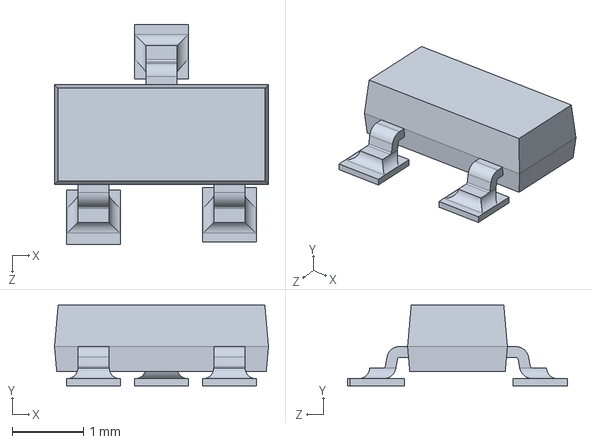
[picture p125: CAD file, 2019-10-08]
STEP AP203/micro ssot3.step
3.00 x 1.13 x 3.09 mm
