guyjeangilles/raspswitch-mirror/STEP AP214/left_face_pcb.step

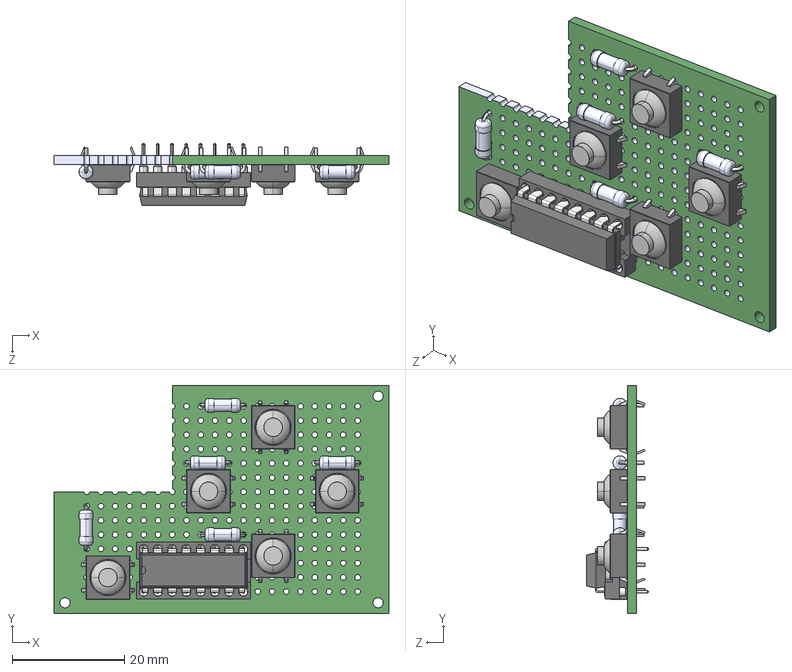
[picture p126: CAD file, 2019-10-08]
STEP AP214/left_face_pcb.step
59.7 x 40.6 x 11.0 mm
Tactal Switch -SOFT -Thru (8mmx 8mmx5.45mm) x 5
