guyjeangilles/raspswitch-mirror/schematics/analog_sticks.sch

## KiCad design schematics/analog_sticks.sch (2019-10-08)

Schematic: analog_sticks.sch

Parts:
U4, U5: ThumbJoystick
