guyjeangilles/raspswitch-mirror/schematics/audio.sch

## KiCad design schematics/audio.sch (2019-10-08)

Schematic: audio.sch

Parts:
J1: AudioJack2_Ground_Switch
J2: Screw_Terminal_01x04
LS1, LS2: Speaker
