guyjeangilles/raspswitch-mirror/schematics/left_face_buttons.sch

## KiCad design schematics/left_face_buttons.sch (2019-10-08)

Schematic: left_face_buttons.sch

Parts:
R8, R9, R10, R11, R12, R13, R14, R15: 10k; R_Axial_DIN0207_L6.3mm_D2.5mm_P7.62mm_Horizontal
SW8, SW9, SW10, SW11, SW13, SW14, SW15: SW_Push; SW_PUSH_8mm
U1: 74LS165; DIP-16_W7.62mm_Socket_with_DIP
