guyjeangilles/raspswitch-mirror/schematics/powersch.sch

## KiCad design schematics/powersch.sch (2019-10-08)

Schematic: powersch.sch

Parts:
D1: LED_RABG
R16: 100
R17: 10k
SW4: SW_SPDT
U6: PowerBoost1000c
