guyjeangilles/raspswitch-mirror/schematics/right_face_buttons.sch

## KiCad design schematics/right_face_buttons.sch (2019-10-08)

Schematic: right_face_buttons.sch

Parts:
R0, R1, R2, R3, R4, R5, R6, R7: 10k; R_Axial_DIN0207_L6.3mm_D2.5mm_P7.62mm_Horizontal
SW0, SW1, SW2, SW3, SW5, SW6, SW7: SW_Push; SW_PUSH_8mm
U0: 74LS165; DIP-16_W7.62mm_Socket_with_DIP
